SolderedElectronics/Li-ion-charger-BQ24295-with-5V-USB-output-board-hardware-design/OUTPUTS/V1.0.0/333075.jpg

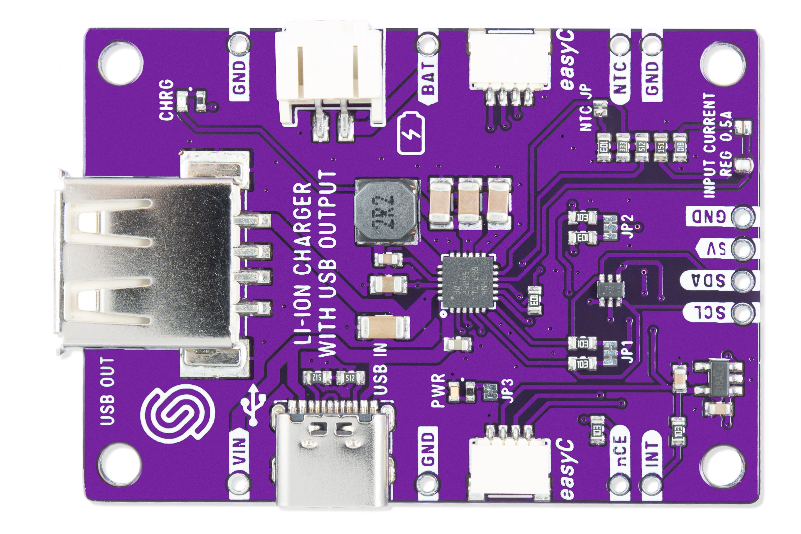
OUTPUTS/V1.0.0/333075.jpg
